matty337s/Wordclock/Docs/Images/img1.png

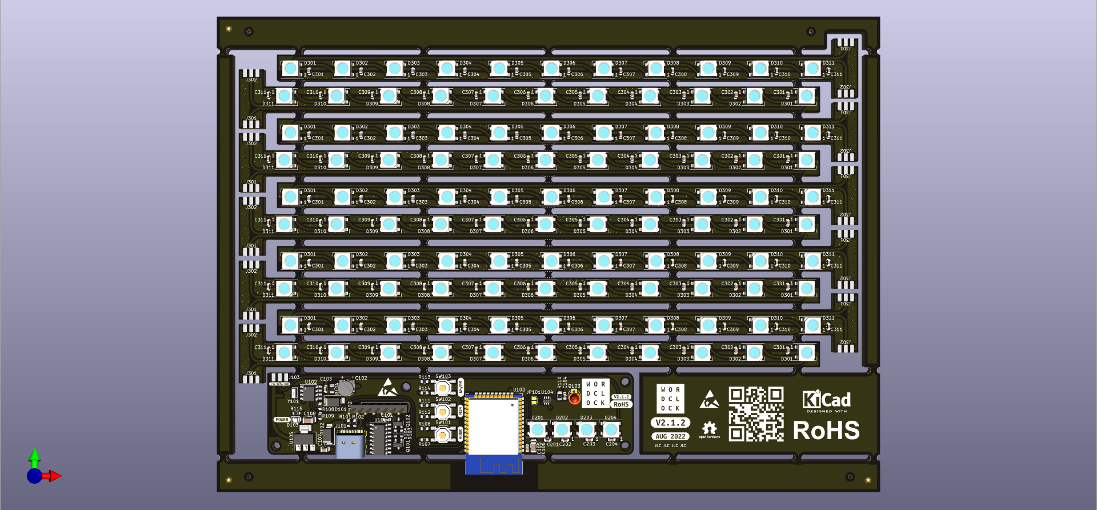
Docs/Images/img1.png
