matty337s/Wordclock/Hardware/Wordclock.kicad_sch

## KiCad design Hardware/Wordclock.kicad_sch (2022-08-30)

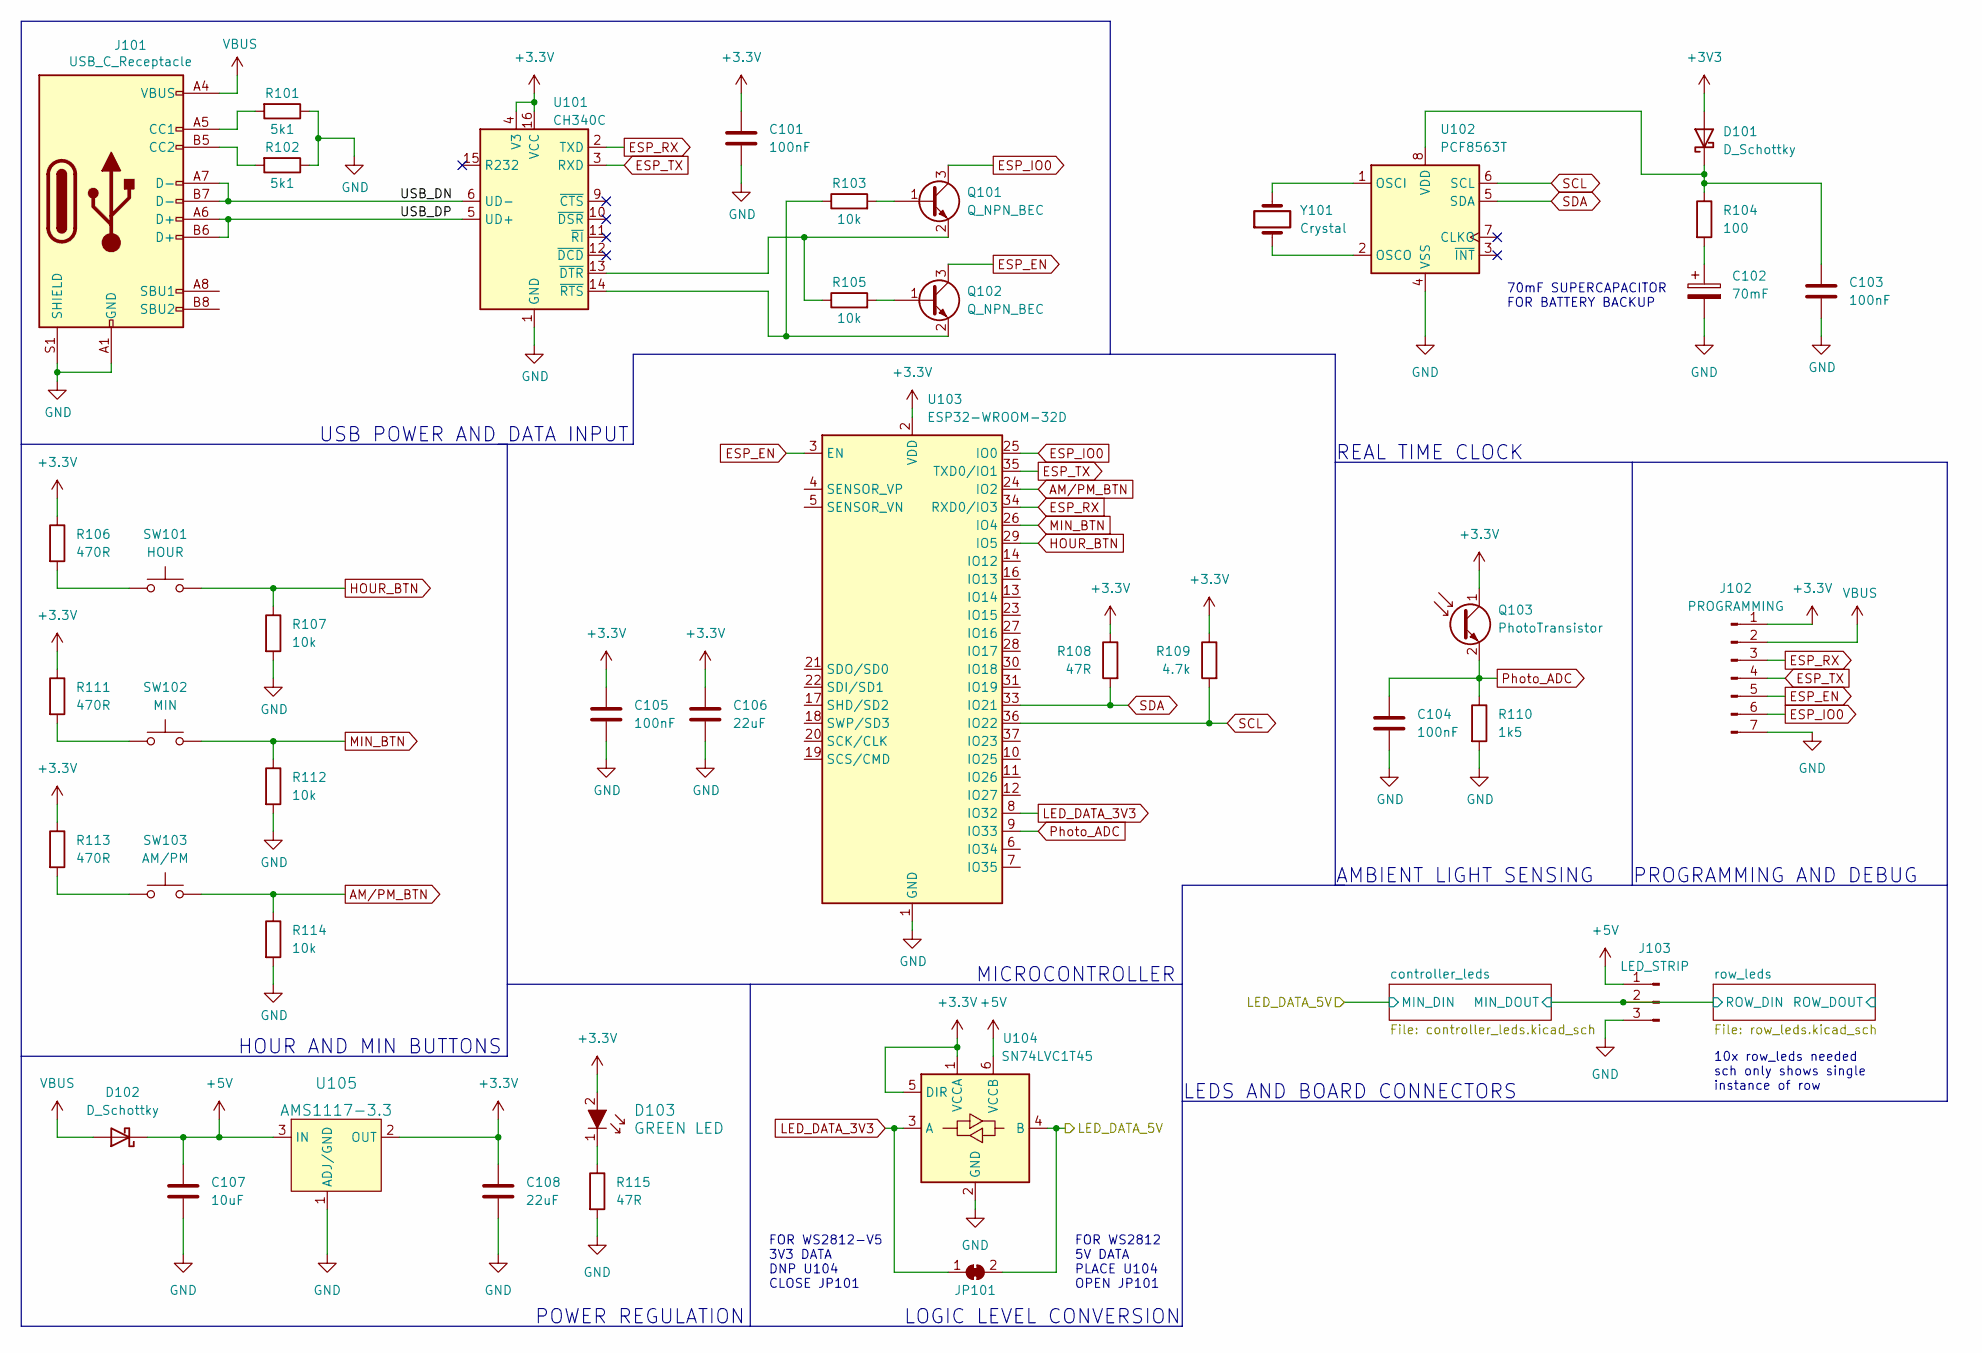
[picture p8: schematic Wordclock.kicad_sch]

Parts:
C101, C103, C104, C105: 100nF; C_0603_1608Metric
C102: 70mF; SM3R3703T01U
C106: 22uF; C_1206_3216Metric; LCSC C8020
C107: 10uF; C_0805_2012Metric
C108: 22uF; C_1206_3216Metric
D101, D102: D_Schottky; D_SMA; LCSC C14996
D103: GREEN LED; LED_0805_2012Metric; MPN LG R971-KN-1; Digi-Key_PN 475-1410-1-ND
J101: USB_C_Receptacle; USB_C_Receptacle_Palconn_UTC16-G; LCSC C167321
J102: PROGRAMMING; PinHeader_1x07_P2.54mm_Vertical
J103: LED_STRIP; PCB_TO_PCB_SOLDER_CONNECTOR
JP101: SolderJumper_2_Bridged; SolderJumper-2_P1.3mm_Bridged_RoundedPad1.0x1.5mm
Q101, Q102: Q_NPN_BEC; SOT-23
Q103: PhotoTransistor; LED_D3.0mm
R101, R102: 5k1; R_0603_1608Metric; LCSC C25905
R103, R105, R107, R112, R114: 10k; R_0603_1608Metric
R104: 100; R_0805_2012Metric
R106, R111, R113: 470R; R_0603_1608Metric
R108, R115: 47R; R_0603_1608Metric
R109: 4.7k; R_0603_1608Metric
R110: 1k5; R_0805_2012Metric
SW101: HOUR; SW_SPST_TL3342; LCSC C318884
SW102: MIN; SW_SPST_TL3342; LCSC C318884
SW103: AM/PM; SW_SPST_TL3342; LCSC C318884
U101: CH340C; SOIC-16_3.9x9.9mm_P1.27mm
U102: PCF8563T; SOIC-8_3.9x4.9mm_P1.27mm
U103: ESP32-WROOM-32D; ESP32-WROOM-32
U104: SN74LVC1T45; SOT-363_SC-70-6
U105: AMS1117-3.3; SOT-223-3_TabPin2; MPN AZ1117CH-3.3TRG1; Digi-Key_PN AZ1117CH-3.3TRG1DICT-ND
Y101: Crystal; Crystal_SMD_3215-2Pin_3.2x1.5mm; LCSC C907543

Connections:
+3.3V: C101.1, C105.1, C106.1, C108.1, D103.2, J102.1, Q103.1 (C), R106.1, R108.1, R109.1, R111.1, R113.1, U101.4 (V3), U101.16 (VCC), U103.2 (VDD), U104.1 (VCCA), U104.5 (DIR), U105.2 (OUT)
+3V3: D101.2 (A)
+5V: C107.1, D102.1 (K), J103.1, U104.6 (VCCB), U105.3 (IN)
AM/PM_BTN: R114.1, SW103.2, U103.24 (IO2)
ESP_EN: J102.5, Q102.3 (C), U103.3 (EN)
ESP_IO0: J102.6, Q101.3 (C), U103.25 (IO0)
ESP_RX: J102.3, U101.2 (TXD), U103.34 (RXD0/IO3)
ESP_TX: J102.4, U101.3 (RXD), U103.35 (TXD0/IO1)
GND: C101.2, C102.2, C103.2, C104.2, C105.2, C106.2, C107.2, C108.2, J101.A1 (GND), J101.A12 (GND), J101.B1 (GND), J101.B12 (GND), J101.S1 (SHIELD), J102.7, J103.3, R101.1, R102.1, R107.2, R110.2, R112.2, R114.2, R115.2, U101.1 (GND), U102.4 (VSS), U103.1 (GND), U103.15 (GND), U103.38 (GND), U103.39 (GND), U104.2 (GND), U105.1 (ADJ/GND)
HOUR_BTN: R107.1, SW101.2, U103.29 (IO5)
LED_DATA_3V3: JP101.1 (A), U103.8 (IO32), U104.3 (A)
LED_DATA_5V: JP101.2 (B), U104.4 (B)
MIN_BTN: R112.1, SW102.2, U103.26 (IO4)
MIN_DOUT: J103.2
unnamed: C102.1, R104.2
unnamed: C103.1, D101.1 (K), R104.1, U102.8 (VDD)
unnamed: D103.1, R115.1
unnamed: J101.A5 (CC1), R101.2
unnamed: J101.B5 (CC2), R102.2
unnamed: Q101.1 (B), R103.2
unnamed: Q101.2 (E), R105.1, U101.13 (~DTR)
unnamed: Q102.1 (B), R105.2
unnamed: Q102.2 (E), R103.1, U101.14 (~RTS)
unnamed: R106.2, SW101.1
unnamed: R111.2, SW102.1
unnamed: R113.2, SW103.1
unnamed: U102.1 (OSCI), Y101.2
unnamed: U102.2 (OSCO), Y101.1
Photo_ADC: C104.1, Q103.2 (E), R110.1, U103.9 (IO33)
SCL: R109.2, U102.6 (SCL), U103.36 (IO22)
SDA: R108.2, U102.5 (SDA), U103.33 (IO21)
USB_DN: J101.A7 (D-), J101.B7 (D-), U101.6 (UD-)
USB_DP: J101.A6 (D+), J101.B6 (D+), U101.5 (UD+)
VBUS: D102.2 (A), J101.A4 (VBUS), J101.A9 (VBUS), J101.B4 (VBUS), J101.B9 (VBUS), J102.2

Notes on the sheet:
REAL TIME CLOCK
AMBIENT LIGHT SENSING
MICROCONTROLLER
70mF SUPERCAPACITOR FOR BATTERY BACKUP
USB POWER AND DATA INPUT
FOR WS2812-V5 3V3 DATA DNP U104 CLOSE JP101
LEDS AND BOARD CONNECTORS
FOR WS2812 5V DATA PLACE U104 OPEN JP101
LOGIC LEVEL CONVERSION
POWER REGULATION
HOUR AND MIN BUTTONS
10x row_leds needed sch only shows single instance of row
PROGRAMMING AND DEBUG
