matty337s/Wordclock/Hardware/controller_leds.kicad_sch

## KiCad design Hardware/controller_leds.kicad_sch (2022-08-28)

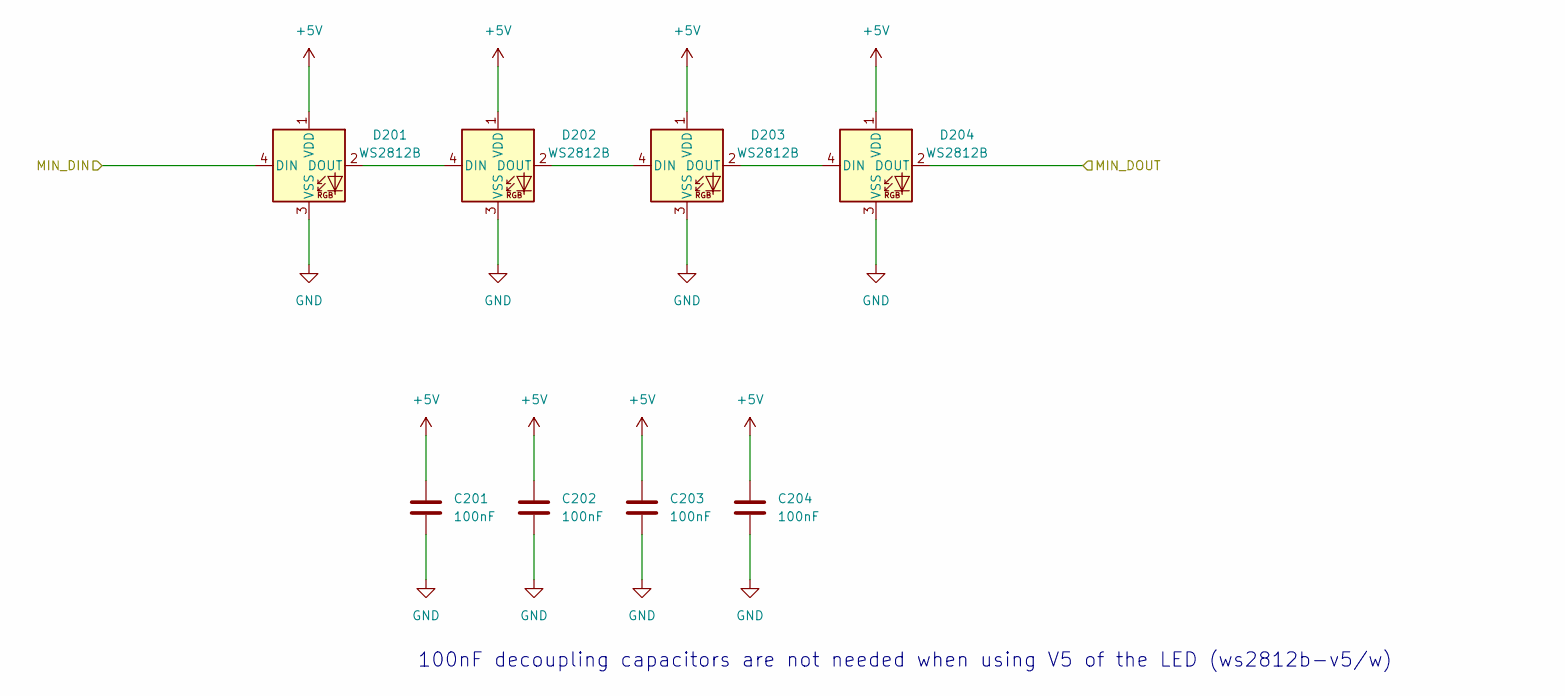
[picture p9: schematic controller_leds.kicad_sch]

Parts:
C201, C202, C203, C204: 100nF; C_0603_1608Metric; LCSC C14663
D201, D202, D203, D204: WS2812B; LED_WS2812B_PLCC4_5.0x5.0mm_P3.2mm; LCSC C14663

Connections:
+5V: C201.1, C202.1, C203.1, C204.1, D201.1 (VDD), D202.1 (VDD), D203.1 (VDD), D204.1 (VDD)
GND: C201.2, C202.2, C203.2, C204.2, D201.3 (VSS), D202.3 (VSS), D203.3 (VSS), D204.3 (VSS)
MIN_DIN: D201.4 (DIN)
MIN_DOUT: D204.2 (DOUT)
unnamed: D201.2 (DOUT), D202.4 (DIN)
unnamed: D202.2 (DOUT), D203.4 (DIN)
unnamed: D203.2 (DOUT), D204.4 (DIN)

Notes on the sheet:
100nF decoupling capacitors are not needed when using V5 of the LED (ws2812b-v5/w)
