matty337s/Wordclock/Hardware/row_leds.kicad_sch

## KiCad design Hardware/row_leds.kicad_sch (2022-08-28)

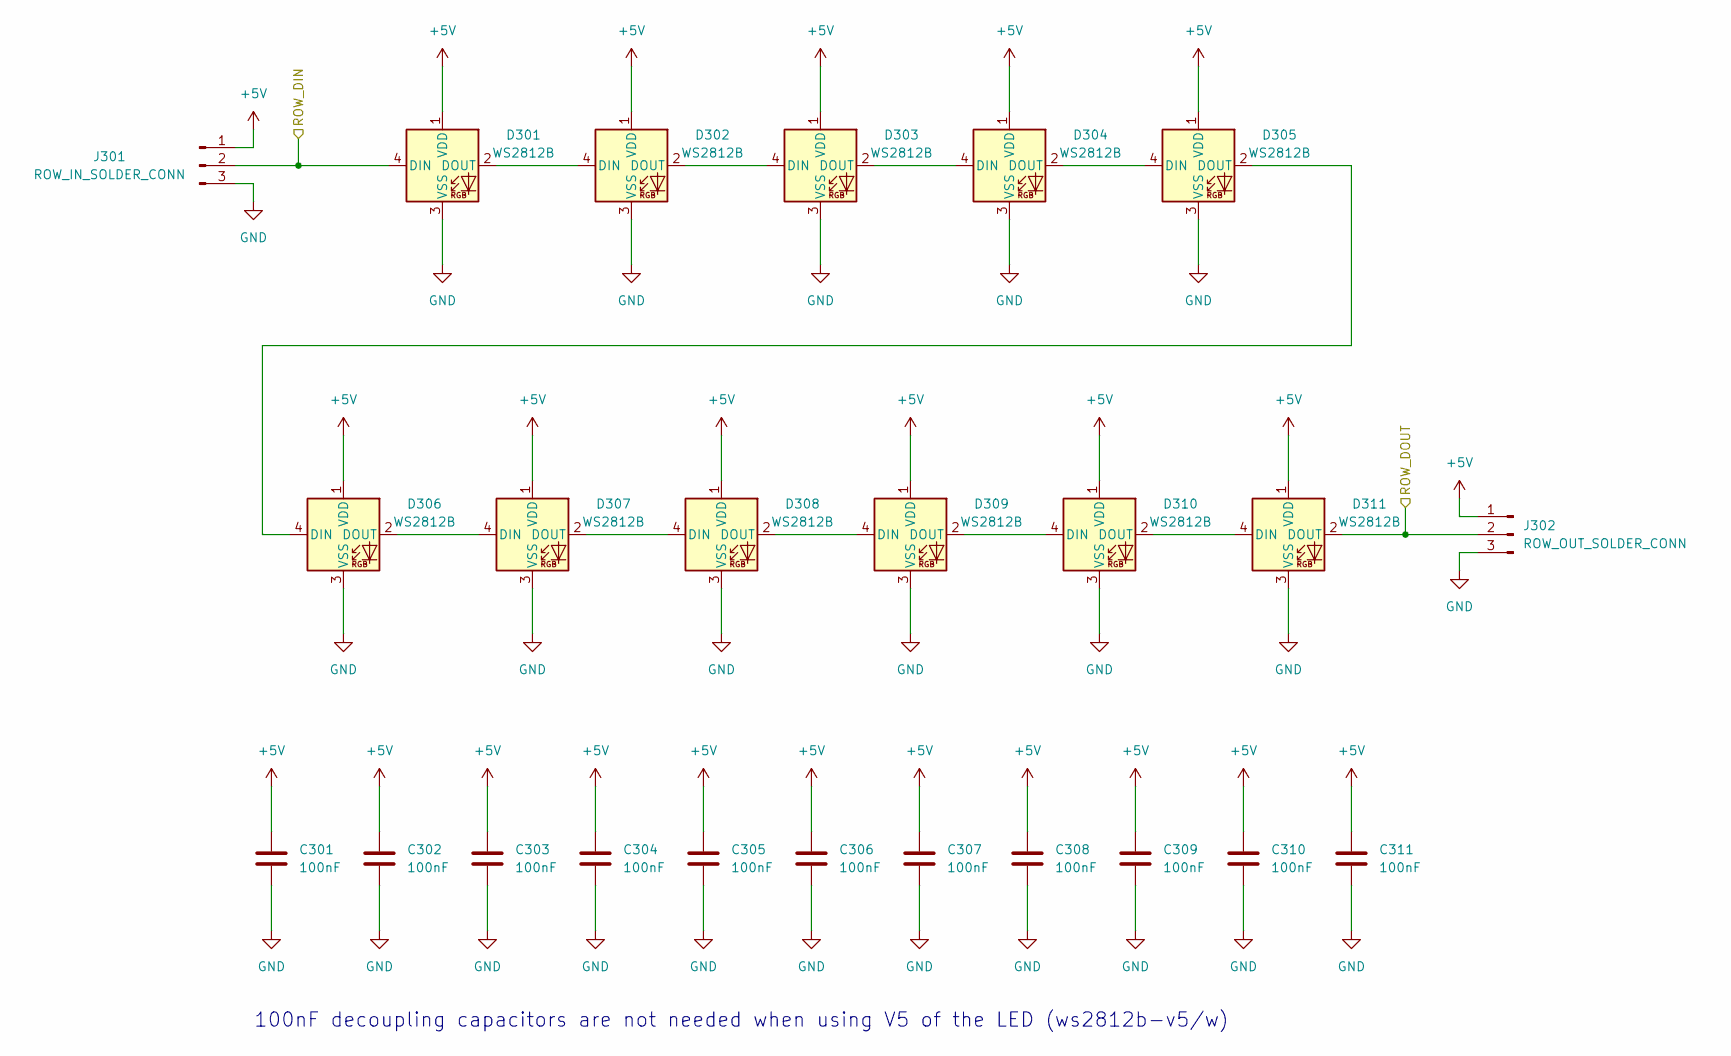
[picture p10: schematic row_leds.kicad_sch]

Parts:
C301, C302, C303, C304, C305, C306, C307, C308, C309, C310, C311: 100nF; C_0603_1608Metric; LCSC C14663
D301, D302, D303, D304, D305, D306, D307, D308, D309, D310, D311: WS2812B; LED_WS2812B_PLCC4_5.0x5.0mm_P3.2mm; LCSC C14663
J301: ROW_IN_SOLDER_CONN; PCB_TO_PCB_SOLDER_CONNECTOR; LCSC C14663
J302: ROW_OUT_SOLDER_CONN; PCB_TO_PCB_SOLDER_CONNECTOR; LCSC C14663

Connections:
+5V: C301.1, C302.1, C303.1, C304.1, C305.1, C306.1, C307.1, C308.1, C309.1, C310.1, C311.1, D301.1 (VDD), D302.1 (VDD), D303.1 (VDD), D304.1 (VDD), D305.1 (VDD), D306.1 (VDD), D307.1 (VDD), D308.1 (VDD), D309.1 (VDD), D310.1 (VDD), D311.1 (VDD), J301.1, J302.1
GND: C301.2, C302.2, C303.2, C304.2, C305.2, C306.2, C307.2, C308.2, C309.2, C310.2, C311.2, D301.3 (VSS), D302.3 (VSS), D303.3 (VSS), D304.3 (VSS), D305.3 (VSS), D306.3 (VSS), D307.3 (VSS), D308.3 (VSS), D309.3 (VSS), D310.3 (VSS), D311.3 (VSS), J301.3, J302.3
unnamed: D301.2 (DOUT), D302.4 (DIN)
unnamed: D302.2 (DOUT), D303.4 (DIN)
unnamed: D303.2 (DOUT), D304.4 (DIN)
unnamed: D304.2 (DOUT), D305.4 (DIN)
unnamed: D305.2 (DOUT), D306.4 (DIN)
unnamed: D306.2 (DOUT), D307.4 (DIN)
unnamed: D307.2 (DOUT), D308.4 (DIN)
unnamed: D308.2 (DOUT), D309.4 (DIN)
unnamed: D309.2 (DOUT), D310.4 (DIN)
unnamed: D310.2 (DOUT), D311.4 (DIN)
ROW_DIN: D301.4 (DIN), J301.2
ROW_DOUT: D311.2 (DOUT), J302.2

Notes on the sheet:
100nF decoupling capacitors are not needed when using V5 of the LED (ws2812b-v5/w)
