matty337s/Wordclock/Firmware/src/ClockFace.h

#pragma once

#include <vector>

class ClockFace
{
public:
  static int pixelCount();

  // The orientation of the clock is infered from where the light sensor is.
  enum class LightSensorPosition
  {
    Bottom,
    Top
  };

  ClockFace(LightSensorPosition position);

  // Rotates the display.
  void setLightSensorPosition(LightSensorPosition position);

  // Updates the state by setting to true all the LEDs that need tobe turned on
  // for the given time. Returns false if there is no change since last update,
  // in which case the state is not updated.
  virtual bool stateForTime(int hour, int minute, int second, bool show_ampm) = 0;

  // Returns the state of all LEDs as pixels. Updated when updateStateForTime()
  // is called.
  const std::vector<bool> &getState() { return _state; };

protected:
  // Lights up a segment in the state.
  void updateSegment(int x, int y, int length);

  // Returns the index of the LED in the strip given a position on the grid.
  uint16_t map(int16_t x, int16_t y);

  uint16_t mapMinute(int corner);

  // To avoid refreshing to often, this stores the time of the previous UI
  // update. If nothing changed, there will be no interuption of animations.
  int _hour, _minute, _second;
  bool _show_ampm;

  LightSensorPosition _position;

  // Stores the bits of the clock that need to be turned on.
  std::vector<bool> _state;
};

class FrenchClockFace : public ClockFace
{
public:
  FrenchClockFace(LightSensorPosition position) : ClockFace(position){};

  virtual bool stateForTime(int hour, int minute, int second, bool show_ampm);
};

class EnglishClockFace : public ClockFace
{
public:
  EnglishClockFace(LightSensorPosition position) : ClockFace(position){};

  virtual bool stateForTime(int hour, int minute, int second, bool show_ampm);
};
